vladimir-aubrecht/Keyboard/firmware/Custom/VaKeyboard/VaKeyboard/Chips/Is31fl3743a.cpp

#include "Is31fl3743a.h"
#include <Adafruit_BusIO_Register.h>

Is31fl3743a::Is31fl3743a(uint8_t i2c_addr, TwoWire* wire, ILogger* logger, uint8_t enabledColumns)
{
	this->i2c_addr = i2c_addr;
	this->wire = wire;
	this->logger = logger;
	this->enabledColumns = enabledColumns;
}

void Is31fl3743a::initialise()
{
	this->i2c_dev = new Adafruit_I2CDevice(this->i2c_addr, this->wire);
	
	if (!this->i2c_dev->begin())
	{
		this->logger->logError("Failed to initialise IS31FL3743A.");
	}

	Adafruit_BusIO_Register CRWL(i2c_dev, 0xFE);
	Adafruit_BusIO_Register CR(i2c_dev, 0xFD);

	CRWL.write(0xC5);	//unlock CR
	CR.write(0x00);	//lets write pwm
	for (int i = 0x01; i < 0xA3; i++)
	{
		uint8_t intensity = random(0xFF);
		intensity = 0xFF;
		Adafruit_BusIO_Register PWM(i2c_dev, i);
		PWM.write(intensity);
	}

	CRWL.write(0xC5);	//unlock CR
	CR.write(0x01);	//lets write scaling
	for (int i = 0x01; i < 0xA3; i++)
	{
		Adafruit_BusIO_Register SL(i2c_dev, i);
		SL.write(0xFF);
	}

	CRWL.write(0xC5);	//unlock CR
	CR.write(0x02);
	Adafruit_BusIO_Register GCC(i2c_dev, 0x01);	//global current
	GCC.write(0xFF);

	uint8_t configuration = (((uint8_t)(11 - this->enabledColumns)) << 4) + 9;
	Adafruit_BusIO_Register CONF(i2c_dev, 0x00);
	CONF.write(configuration);  //normal mode + enabled columns

	Adafruit_BusIO_Register PDU(i2c_dev, 0x02);
	PDU.write(0b00110011);

	Adafruit_BusIO_Register SS(i2c_dev, 0x25);
	SS.write(0b00000001);	//configure timing to 1200 us
}
