vladimir-aubrecht/Keyboard/firmware/Custom/VaKeyboard/VaKeyboard/Chips/Is31fl3743a.h

#pragma once
#include <Wire.h>
#include <arduino.h>
#include <Adafruit_I2CDevice.h>

#include "ILogger.h"

class Is31fl3743a
{
private:
	uint8_t i2c_addr = 0;
	TwoWire* wire = NULL;
	Adafruit_I2CDevice* i2c_dev = NULL;
	ILogger* logger = NULL;
	uint8_t enabledColumns = 0;

public:
	Is31fl3743a(uint8_t i2c_addr, TwoWire* wire, ILogger* logger, uint8_t enabledColumns);

	void initialise();
};
